Tinkerforge/master-brick/software/src/extensions/ethernet/ethernet_config.h

/* master-brick
 * Copyright (C) 2012-2014 Olaf Lüke <olaf@tinkerforge.com>
 *
 * ethernet_config.h: Configuration of Ethernet implementation
 *
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
 * You should have received a copy of the GNU Lesser General Public
 * License along with this library; if not, write to the
 * Free Software Foundation, Inc., 59 Temple Place - Suite 330,
 * Boston, MA 02111-1307, USA.
 */

#ifndef ETHERNET_CONFIG_H
#define ETHERNET_CONFIG_H

#include "bricklib/logging/logging.h"

#define ETHERNET_KEY (42 | (23 << 8) | (17 << 16) | (8 << 24))
#define ETHERNET_KEY_POS 4
#define ETHERNET_CONFIGURATION_POS 8
#define ETHERNET_HOSTNAME_POS (ETHERNET_CONFIGURATION_POS + sizeof(SetEthernetConfiguration) - sizeof(MessageHeader))
#define ETHERNET_WEBSOCKET_CONFIGURATION_POS (ETHERNET_HOSTNAME_POS + sizeof(SetEthernetHostname) - sizeof(MessageHeader))
#define ETHERNET_AUTHENTICATION_SECRET_KEY_POS (ETHERNET_WEBSOCKET_CONFIGURATION_POS + sizeof(SetEthernetWebsocketConfiguration) - sizeof(MessageHeader))
#define ETHERNET_AUTHENTICATION_SECRET_POS (4 + ETHERNET_AUTHENTICATION_SECRET_KEY_POS)
#define ETHERNET_MAC_POS (32*4)

#define ETHERNET_HOSTNAME_LENGTH 32

#define ETHERNET_CONNECTION_DHCP 0
#define ETHERNET_CONNECTION_STATIC 1

#define ETHERNET_MAX_DATA_LENGTH 80
#define ETHERNET_MAX_SOCKETS 7
#define ETHERNET_BUFFER_SIZE WIFI_MAX_DATA_LENGTH
#define ETHERNET_UDP_HEADER_SIZE 8

#define ETHERNET_USART_SPI_CLOCK 2000000

#define ETHERNET_W5200_READ_COMMAND    0x00
#define ETHERNET_W5200_WRITE_COMMAND   0x80
#define ETHERNET_W5500_READ_COMMAND    0x00
#define ETHERNET_W5500_WRITE_COMMAND   0x04

#define ETHERNET_CS_0        0
#define ETHERNET_CS_1        4
#define ETHERNET_RESET_0     1
#define ETHERNET_RESET_1     5
#define ETHERNET_INT_0       2
#define ETHERNET_INT_1       6
#define ETHERNET_PWDN_0      3
#define ETHERNET_PWDN_1      7

#define ETHERNET_MISO        8
#define ETHERNET_MOSI        9
#define ETHERNET_CLK        10

#define ETHERNET_RX_SIZE     2
#define ETHERNET_TX_SIZE     2
#define ETHERNET_MAC_SIZE    6
#define ETHERNET_IP_SIZE     4
#define ETHERNET_NUM_SOCKETS 8

#define ETHERNET_RX_BASE 0xC000
#define ETHERNET_TX_BASE 0x8000
#define ETHERNET_RX_MASK 0x07FF
#define ETHERNET_TX_MASK 0x07FF


#define DEBUG_ETHERNET 1

#if(DEBUG_ETHERNET)
#define logethd(str, ...) do{logd("eth: " str, ##__VA_ARGS__);}while(0)
#define logethi(str, ...) do{logi("eth: " str, ##__VA_ARGS__);}while(0)
#define logethw(str, ...) do{logw("eth: " str, ##__VA_ARGS__);}while(0)
#define logethe(str, ...) do{loge("eth: " str, ##__VA_ARGS__);}while(0)
#define logethf(str, ...) do{logf("eth: " str, ##__VA_ARGS__);}while(0)
#else
#define logethd(str, ...) {}
#define logethi(str, ...) {}
#define logethw(str, ...) {}
#define logethe(str, ...) {}
#define logethf(str, ...) {}
#endif

#endif
