Tinkerforge/master-brick/software/src/extensions/ethernet/ethernet_websocket.c

/* master-brick
 * Copyright (C) 2014 Olaf Lüke <olaf@tinkerforge.com>
 *
 * ethernet_websocket.c: Ethernet websocket implementation
 *
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
 * You should have received a copy of the GNU Lesser General Public
 * License along with this library; if not, write to the
 * Free Software Foundation, Inc., 59 Temple Place - Suite 330,
 * Boston, MA 02111-1307, USA.
 */

#include "ethernet_websocket.h"

#include <stdint.h>
#include <stdbool.h>
#include <string.h>

#include "config.h"
#include "ethernet_config.h"
#include "ethernet_low_level.h"
#include "extensions/websocket.h"
#include "extensions/brickd.h"

extern ComInfo com_info;

EthernetWebsocketState ethernet_websocket_state[ETHERNET_MAX_SOCKETS] = {
	WEBSOCKET_STATE_WAIT_FOR_HANDSHAKE,
	WEBSOCKET_STATE_WAIT_FOR_HANDSHAKE,
	WEBSOCKET_STATE_WAIT_FOR_HANDSHAKE,
	WEBSOCKET_STATE_WAIT_FOR_HANDSHAKE,
	WEBSOCKET_STATE_WAIT_FOR_HANDSHAKE,
	WEBSOCKET_STATE_WAIT_FOR_HANDSHAKE,
	WEBSOCKET_STATE_WAIT_FOR_HANDSHAKE
};

WebsocketFrame ethernet_websocket_frame[ETHERNET_MAX_SOCKETS] = {{0}};

uint8_t ethernet_websocket_to_read[ETHERNET_MAX_SOCKETS] = {0, 0, 0, 0, 0, 0, 0};
uint8_t ethernet_websocket_mask_mod[ETHERNET_MAX_SOCKETS] = {0, 0, 0, 0, 0, 0, 0};

#define ETHERNET_WEBSOCKET_ERROR_ANSWER_1 "HTTP/1.1 200 OK\r\nContent-Length: 276\r\nContent-Type: text/html\r\n\r\n"
#define ETHERNET_WEBSOCKET_ERROR_ANSWER_2 "<html><head><title>This is a Websocket</title></head><body>Dear Sir or Madam,<br/><br/>I regret to inform you that there is no webserver "
#define ETHERNET_WEBSOCKET_ERROR_ANSWER_3 "here.<br/>This port is exclusively used for Websockets.<br/><br/>Yours faithfully,<blockquote>Ethernet Extension</blockquote></body></html>"

void ethernet_websocket_init(const uint8_t socket) {
	ethernet_websocket_state[socket] = WEBSOCKET_STATE_WAIT_FOR_HANDSHAKE;
	ethernet_websocket_to_read[socket] = 0;
	ethernet_websocket_frame[socket].fin = 0;
	ethernet_websocket_frame[socket].mask = 0;
	ethernet_websocket_frame[socket].rsv1 = 0;
	ethernet_websocket_frame[socket].rsv2 = 0;
	ethernet_websocket_frame[socket].rsv3 = 0;
	ethernet_websocket_frame[socket].opcode = 0;
	ethernet_websocket_frame[socket].payload_length = 0;
	ethernet_websocket_frame[socket].masking_key[0] = 0;
	ethernet_websocket_frame[socket].masking_key[1] = 0;
	ethernet_websocket_frame[socket].masking_key[2] = 0;
	ethernet_websocket_frame[socket].masking_key[3] = 0;
}

void ethernet_websocket_answer_error(int32_t user_data) {
	if(user_data > 7) {
		return;
	}

	ethernet_low_level_write_data_tcp_blocking(user_data, (uint8_t*)ETHERNET_WEBSOCKET_ERROR_ANSWER_1, strlen(ETHERNET_WEBSOCKET_ERROR_ANSWER_1));
	ethernet_low_level_write_data_tcp_blocking(user_data, (uint8_t*)ETHERNET_WEBSOCKET_ERROR_ANSWER_2, strlen(ETHERNET_WEBSOCKET_ERROR_ANSWER_2));
	ethernet_low_level_write_data_tcp_blocking(user_data, (uint8_t*)ETHERNET_WEBSOCKET_ERROR_ANSWER_3, strlen(ETHERNET_WEBSOCKET_ERROR_ANSWER_3));
	ethernet_low_level_emergency_disconnect(user_data);
}

void ethernet_websocket_answer_callback(char *answer, uint8_t length, int32_t user_data) {
	if(user_data > 7) {
		return;
	}

	ethernet_low_level_write_data_tcp_blocking(user_data, (uint8_t*)WEBSOCKET_ANSWER_STRING_1, strlen(WEBSOCKET_ANSWER_STRING_1));
	ethernet_low_level_write_data_tcp_blocking(user_data, (uint8_t*)answer, length);
	ethernet_low_level_write_data_tcp_blocking(user_data, (uint8_t*)WEBSOCKET_ANSWER_STRING_2, strlen(WEBSOCKET_ANSWER_STRING_2));
	ethernet_websocket_state[user_data] = WEBSOCKET_STATE_HANDSHAKE_DONE;
	ethernet_websocket_to_read[user_data] = sizeof(WebsocketFrame);

	com_info.current = COM_ETHERNET;
}

uint8_t ethernet_websocket_write_data_tcp(const uint8_t socket, const uint8_t *buffer, const uint8_t length) {
	WebsocketFrameClientToServer wfcts;
	wfcts.fin = 1;
	wfcts.rsv1 = 0;
	wfcts.rsv2 = 0;
	wfcts.rsv3 = 0;
	wfcts.opcode = 2;
	wfcts.mask = 0;
	wfcts.payload_length = length;

	uint8_t length_to_send = sizeof(WebsocketFrameClientToServer) + length;
	uint8_t websocket_data[length_to_send];
	memcpy((void*)websocket_data, (void*)&wfcts, sizeof(WebsocketFrameClientToServer));
	memcpy((void*)(websocket_data + sizeof(WebsocketFrameClientToServer)), buffer, length);

	// For websockets we have to send the whole data package, otherwise
	// we may send the header more then once
	ethernet_low_level_write_data_tcp_blocking(socket, websocket_data, length_to_send);

	return length;
}

void ethernet_websocket_close_frame(const WebsocketFrame *wsf, const uint8_t socket) {
	uint8_t length = wsf->payload_length;
	uint8_t tmp_buffer[length];
	while(length > 0) {
		length -= ethernet_low_level_read_data_tcp(socket, tmp_buffer, length);
	}
	ethernet_low_level_disconnect(socket);
	brickd_disconnect(socket);

	ethernet_low_level_socket_init(socket);
	ethernet_low_level_socket_listen(socket);
	brickd_disconnect(socket);
}

uint8_t ethernet_websocket_read_data_tcp(const uint8_t socket, uint8_t *buffer, const uint8_t length) {
	uint8_t read_length = 0;
	switch(ethernet_websocket_state[socket]) {
		case WEBSOCKET_STATE_WAIT_FOR_HANDSHAKE: {
			uint8_t data[100];
			uint8_t handshake_length = ethernet_low_level_read_data_tcp(socket, data, 100);
			if(handshake_length != 0) {
				websocket_parse_handshake((char*)data, handshake_length, ethernet_websocket_answer_callback, ethernet_websocket_answer_error, socket);
			}

			return 0;
		}

		case WEBSOCKET_STATE_HANDSHAKE_DONE: {
			// buffer with max possible size of websocket header
			ethernet_websocket_frame[socket].fin = 1;
			ethernet_websocket_to_read[socket] -= ethernet_low_level_read_data_tcp(socket,
			                                                                       ((uint8_t*)&ethernet_websocket_frame[socket]) + (sizeof(WebsocketFrame) - ethernet_websocket_to_read[socket]),
			                                                                       ethernet_websocket_to_read[socket]);

			if(ethernet_websocket_to_read[socket] != 0) {
				return 0;
			}

			ethernet_websocket_state[socket] = WEBSOCKET_STATE_WEBSOCKET_HEADER_DONE;

			if(ethernet_websocket_frame[socket].mask != 1) {
				// mask = 0 from browser is not allowed!
				logethe("Mask=0 not allowed\n\r");
				ethernet_low_level_emergency_disconnect(socket);
				return 0;
			}

			// We currently don't support 16 bit or 64 bit length
			if(ethernet_websocket_frame[socket].payload_length == 126 || ethernet_websocket_frame[socket].payload_length == 127) {
				ethernet_low_level_emergency_disconnect(socket);
				return 0;
			}

			switch(ethernet_websocket_frame[socket].opcode) {
				case WEBSOCKET_OPCODE_CONTINUATION_FRAME:
				case WEBSOCKET_OPCODE_TEXT_FRAME: {
					// Continuation and text frame not allowed
					logethe("Opcode not supported: %d\n\r", ethernet_websocket_frame[socket].opcode);
					ethernet_low_level_emergency_disconnect(socket);
					return 0;
				}

				case WEBSOCKET_OPCODE_BINARY_FRAME: {
					ethernet_websocket_mask_mod[socket] = 0;
					ethernet_websocket_to_read[socket] = ethernet_websocket_frame[socket].payload_length;
					break;
				}

				case WEBSOCKET_OPCODE_CLOSE_FRAME: {
					ethernet_websocket_close_frame(&ethernet_websocket_frame[socket], socket);
					break;
				}

				case WEBSOCKET_OPCODE_PING_FRAME: {
					logethe("Opcode not supported: %d\n\r", ethernet_websocket_frame[socket].opcode);
					ethernet_low_level_emergency_disconnect(socket);
					break;
				}

				case WEBSCOKET_OPCODE_PONG_FRAME: {
					logethe("Opcode not supported: %d\n\r", ethernet_websocket_frame[socket].opcode);
					ethernet_low_level_emergency_disconnect(socket);
					break;
				}
			}

			return 0;
		}

		case WEBSOCKET_STATE_WEBSOCKET_HEADER_DONE: {
			// Websocket header is done, we can just read the data
			read_length = ethernet_low_level_read_data_tcp(socket, buffer, MIN(length, ethernet_websocket_to_read[socket]));

			for(uint8_t i = 0; i < read_length; i++) {
				buffer[i] ^= ethernet_websocket_frame[socket].masking_key[ethernet_websocket_mask_mod[socket]];
				ethernet_websocket_mask_mod[socket]++;
				if(ethernet_websocket_mask_mod[socket] >= WEBSOCKET_MASK_LENGTH) {
					ethernet_websocket_mask_mod[socket] = 0;
				}
			}

			ethernet_websocket_to_read[socket] -= read_length;
			if(ethernet_websocket_to_read[socket] == 0) {
				ethernet_websocket_state[socket] = WEBSOCKET_STATE_HANDSHAKE_DONE;
				ethernet_websocket_to_read[socket] = sizeof(WebsocketFrame);
			}

			break;
		}

		default: {
			logethe("Invalid Ethernet Websocket state: %d\n\r", (int)ethernet_websocket_state);
			break;
		}
	}

	return read_length;
}
