Tinkerforge/master-brick/software/src/extensions/ethernet/ethernet_low_level.h

/* master-brick
 * Copyright (C) 2012-2014 Olaf Lüke <olaf@tinkerforge.com>
 *
 * ethernet_low_level.h: Low level Ethernet protocol implementation
 *
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
 * You should have received a copy of the GNU Lesser General Public
 * License along with this library; if not, write to the
 * Free Software Foundation, Inc., 59 Temple Place - Suite 330,
 * Boston, MA 02111-1307, USA.
 */

#ifndef ETHERNET_LOW_LEVEL_H
#define ETHERNET_LOW_LEVEL_H

#include <stdint.h>

#include "ethernet_config.h"

typedef struct {
	uint32_t ETH_REG_MODE;
	uint32_t ETH_REG_GATEWAY_ADDRESS;
	uint32_t ETH_REG_SUBNET_MASK;
	uint32_t ETH_REG_SOURCE_HW_ADDRESS;
	uint32_t ETH_REG_SOURCE_IP_ADDRESS;
	uint32_t ETH_REG_RETRY_TIME;
	uint32_t ETH_REG_RETRY_COUNT;
	uint32_t ETH_REG_CHIP_VERSION;
	uint32_t CH_BASE;
	uint32_t CH_OFFSET_SHIFT;
} W5X00Register;

#define W5500_BSB_TX(s) ((2 + ((s) << 2)) << 3)
#define W5500_BSB_RX(s) ((3 + ((s) << 2)) << 3)

// Leave registers here for reference.
// We only put registers in the struct above if they are used, this saves space.
#if 0
#define ETH_REG_MODE                   0x0000
#define ETH_REG_GATEWAY_ADDRESS        0x0001
#define ETH_REG_SUBNET_MASK            0x0005
#define ETH_REG_SOURCE_HW_ADDRESS      0x0009
#define ETH_REG_SOURCE_IP_ADDRESS      0x000F
#define ETH_REG_INTERRUPT              0x0015
#define ETH_REG_INTERRUPT_MASK         0x0016
#define ETH_REG_RETRY_TIME             0x0017
#define ETH_REG_RETRY_COUNT            0x0019
#define ETH_REG_AUTH_TYPE              0x001C
#define ETH_REG_AUTH_ALGORITHM         0x001E
#define ETH_REG_CHIP_VERSION           0x001F
#define ETH_REG_PPP_LCP_REQUEST_TIMER  0x0028
#define ETH_REG_PPP_LCP_MAGIC_NUMBER   0x0029
#define ETH_REG_INTERRUPT_LOW_LEVEL    0x0030
#define ETH_REG_SOCKET_INTERRUPT       0x0034
#define ETH_REG_PHY_STATUS             0x0035
#define ETH_REG_SOCKET_INTERRUPT_MASK  0x0036
#endif

#define ETH_REG_OFFSET(s)               ((ethernet_regs->CH_BASE) + ((s) << (ethernet_regs->CH_OFFSET_SHIFT)))
#define ETH_REG_SN_MR(s)                (ETH_REG_OFFSET(s) + 0x000000)
#define ETH_REG_SN_CR(s)                (ETH_REG_OFFSET(s) + 0x000100)
#define ETH_REG_SN_IR(s)                (ETH_REG_OFFSET(s) + 0x000200)
#define ETH_REG_SN_SR(s)                (ETH_REG_OFFSET(s) + 0x000300)
#define ETH_REG_SN_PORT(s)              (ETH_REG_OFFSET(s) + 0x000400)
#define ETH_REG_SN_DHAR(s)              (ETH_REG_OFFSET(s) + 0x000600)
#define ETH_REG_SN_DIPR(s)              (ETH_REG_OFFSET(s) + 0x000C00)
#define ETH_REG_SN_DPORT(s)             (ETH_REG_OFFSET(s) + 0x001000)
#define ETH_REG_SN_MSSR(s)              (ETH_REG_OFFSET(s) + 0x001200)
#define ETH_REG_SN_PROTO(s)             (ETH_REG_OFFSET(s) + 0x001400)
#define ETH_REG_SN_TOS(s)               (ETH_REG_OFFSET(s) + 0x001500)
#define ETH_REG_SN_TTL(s)               (ETH_REG_OFFSET(s) + 0x001600)
#define ETH_REG_SN_RXMEM_SIZE(s)        (ETH_REG_OFFSET(s) + 0x001E00)
#define ETH_REG_SN_TXMEM_SIZE(s)        (ETH_REG_OFFSET(s) + 0x001F00)
#define ETH_REG_SN_TX_FSR(s)            (ETH_REG_OFFSET(s) + 0x002000)
#define ETH_REG_SN_TX_RD(s)             (ETH_REG_OFFSET(s) + 0x002200)
#define ETH_REG_SN_TX_WR(s)             (ETH_REG_OFFSET(s) + 0x002400)
#define ETH_REG_SN_RX_RSR(s)            (ETH_REG_OFFSET(s) + 0x002600)
#define ETH_REG_SN_RX_RD(s)             (ETH_REG_OFFSET(s) + 0x002800)
#define ETH_REG_SN_RX_WR(s)             (ETH_REG_OFFSET(s) + 0x002A00)
#define ETH_REG_SN_IMR(s)               (ETH_REG_OFFSET(s) + 0x002C00)
#define ETH_REG_SN_FRAG(s)              (ETH_REG_OFFSET(s) + 0x002D00)

#define ETH_VAL_MODE_SW_RESET          (1 << 7)
#define ETH_VAL_MODE_PB                (1 << 6)
#define ETH_VAL_MODE_PPOE              (1 << 3)

#define ETH_VAL_PHY_STATUS_LINK        (1 << 5)
#define ETH_VAL_PHY_STATUS_POWERDOWN   (1 << 3)

#define ETH_VAL_SN_MR_MULTI            (1 << 7)
#define ETH_VAL_SN_MR_MF               (1 << 6)
#define ETH_VAL_SN_MR_ND_MC            (1 << 5)
#define ETH_VAL_SN_MR_PROTO_CLOSED     (0 << 0)
#define ETH_VAL_SN_MR_PROTO_TCP        (1 << 0)
#define ETH_VAL_SN_MR_PROTO_UDP        (2 << 0)
#define ETH_VAL_SN_MR_PROTO_IPRAW      (3 << 0)
#define ETH_VAL_SN_MR_PROTO_MACRAW     (4 << 0)
#define ETH_VAL_SN_MR_PROTO_PPPOE      (5 << 0)


#define ETH_VAL_SN_CR_OPEN             0x01
#define ETH_VAL_SN_CR_LISTEN           0x02
#define ETH_VAL_SN_CR_CONNECT          0x04
#define ETH_VAL_SN_CR_DISCON           0x08
#define ETH_VAL_SN_CR_CLOSE            0x10
#define ETH_VAL_SN_CR_SEND             0x20
#define ETH_VAL_SN_CR_SEND_MAC         0x21
#define ETH_VAL_SN_CR_SEND_KEEP        0x22
#define ETH_VAL_SN_CR_RECV             0x40

#define ETH_VAL_SN_IR_PRECV            (1 << 7)
#define ETH_VAL_SN_IR_PFAIL            (1 << 6)
#define ETH_VAL_SN_IR_PNEXT            (1 << 5)
#define ETH_VAL_SN_IR_SEND_OK          (1 << 4)
#define ETH_VAL_SN_IR_TIMEOUT          (1 << 3)
#define ETH_VAL_SN_IR_RECV             (1 << 2)
#define ETH_VAL_SN_IR_DISCON           (1 << 1)
#define ETH_VAL_SN_IR_CON              (1 << 0)

#define ETH_VAL_SN_SR_SOCK_CLOSED      0x00
#define ETH_VAL_SN_SR_SOCK_INIT        0x13
#define ETH_VAL_SN_SR_SOCK_LISTEN      0x14
#define ETH_VAL_SN_SR_SOCK_ESTABLISHED 0x17
#define ETH_VAL_SN_SR_SOCK_CLOSE_WAIT  0x1C
#define ETH_VAL_SN_SR_SOCK_UDP         0x22
#define ETH_VAL_SN_SR_SOCK_IPRAW       0x32
#define ETH_VAL_SN_SR_SOCK_MACRAW      0x42
#define ETH_VAL_SN_SR_SOCK_PPOE        0x5F
#define ETH_VAL_SN_SR_SOCK_SYNSENT     0x15
#define ETH_VAL_SN_SR_SOCK_SYNRECV     0x16
#define ETH_VAL_SN_SR_SOCK_FIN_WAIT    0x18
#define ETH_VAL_SN_SR_SOCK_CLOSING     0x1A
#define ETH_VAL_SN_SR_SOCK_TIME_WAIT   0x1B
#define ETH_VAL_SN_SR_SOCK_LAST_ACK    0x1D
#define ETH_VAL_SN_SR_SOCK_ARP         0x01

#define ETH_VAL_SN_IMR_PRECV           (1 << 7)
#define ETH_VAL_SN_IMR_PFAIL           (1 << 6)
#define ETH_VAL_SN_IMR_PNEXT           (1 << 5)
#define ETH_VAL_SN_IMR_SENDOK          (1 << 4)
#define ETH_VAL_SN_IMR_TIMEOUT         (1 << 3)
#define ETH_VAL_SN_IMR_RECV            (1 << 2)
#define ETH_VAL_SN_IMR_DISCON          (1 << 1)
#define ETH_VAL_SN_IMR_CON             (1 << 0)

void ethernet_low_level_get_default_hostname(char hostname[ETHERNET_HOSTNAME_LENGTH]);
void ethernet_low_level_reset(void);
void ethernet_low_level_init(void);
void ethernet_low_level_check_config(void);
bool ethernet_low_level_discover_chip_version(void);
void ethernet_low_level_emergency_disconnect(const uint8_t socket);
void ethernet_low_level_disconnect(const uint8_t socket);
uint8_t ethernet_low_level_get_status(const uint8_t socket);
void ethernet_low_level_socket_init(const uint8_t socket);
void ethernet_low_level_socket_listen(const uint8_t socket);
uint16_t ethernet_low_level_get_received_data_length(const uint8_t socket);
uint16_t ethernet_low_level_get_free_data_length(const uint8_t socket);
uint16_t ethernet_low_level_get_transmit_pointer(const uint8_t socket);
void ethernet_low_level_set_transmit_pointer(const uint8_t socket, const uint16_t pointer);
uint8_t ethernet_low_level_write_data_tcp_blocking(const uint8_t socket, const uint8_t *buffer, const uint8_t length);
uint8_t ethernet_low_level_read_data_tcp(const uint8_t socket, uint8_t *buffer, const uint8_t length);
uint8_t ethernet_low_level_write_data_tcp(const uint8_t socket, const uint8_t *buffer, const uint8_t length);
uint16_t ethernet_low_level_read_data_udp(const uint8_t socket, uint8_t *buffer, const uint16_t length, uint8_t ip[4], uint16_t *port);
uint16_t ethernet_low_level_write_data_udp(const uint8_t socket, const uint8_t *buffer, const uint16_t length, const uint8_t ip[4], const uint16_t port);
uint16_t ethernet_low_level_get_receive_pointer(const uint8_t socket);
void ethernet_low_level_set_receive_pointer(const uint8_t socket, const uint16_t pointer);
void ethernet_low_level_set_retry_time(const uint16_t retry_time);
void ethernet_low_level_set_retry_count(const uint8_t retry_count);
void ethernet_select(void);
void ethernet_deselect(void);
uint8_t ethernet_transceive_byte(const uint8_t value);
uint8_t ethernet_read_register(const uint32_t address);
void ethernet_write_register(const uint32_t address, const uint8_t value);
extern uint8_t (*ethernet_read_buffer)(const uint32_t address, uint8_t *buffer, const uint16_t length);
extern uint8_t (*ethernet_write_buffer)(const uint32_t address, const uint8_t *buffer, const uint16_t length);

#endif
