Tinkerforge/master-brick/software/src/extensions/ethernet/ethernet_dhcp.h

/* master-brick
 * Copyright (C) 2012 Olaf Lüke <olaf@tinkerforge.com>
 *
 * ethernet_dhcp.h: DHCP implementation for Ethernet Extension
 *
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
 * You should have received a copy of the GNU Lesser General Public
 * License along with this library; if not, write to the
 * Free Software Foundation, Inc., 59 Temple Place - Suite 330,
 * Boston, MA 02111-1307, USA.
 */

#ifndef ETHERNET_DHCP_H
#define ETHERNET_DHCP_H

#include <stdint.h>
#include <stdbool.h>

#define DHCP_SOCKET             7

// DHCP state machine
#define	STATE_DHCP_DISCOVER	    1
#define	STATE_DHCP_REQUEST      2
#define	STATE_DHCP_LEASED       3
#define	STATE_DHCP_REREQUEST    4
#define	STATE_DHCP_RELEASE      5

#define	DHCP_MAX_RETRY          3
#define	DHCP_WAIT_TIME          5

#define DHCP_FLAGSBROADCAST     0x8000

// UDP port numbers for DHCP
#define	DHCP_SERVER_PORT        67 // from server to client
#define DHCP_CLIENT_PORT        68 // from client to server

// DHCP message OP code
#define DHCP_BOOTREQUEST        1
#define DHCP_BOOTREPLY          2

// DHCP message type
#define	DHCP_DISCOVER           1
#define DHCP_OFFER              2
#define	DHCP_REQUEST            3
#define	DHCP_DECLINE            4
#define	DHCP_ACK                5
#define DHCP_NAK                6
#define	DHCP_RELEASE            7
#define DHCP_INFORM             8

// DHCP retransmission timeout (ms)
#define DHCP_INITIAL_RTO        ( 4*1000000)
#define DHCP_MAX_RTO            (64*1000000)

#define DHCP_HTYPE10MB          1
#define DHCP_HTYPE100MB         2

#define DHCP_HLENETHERNET       6
#define DHCP_HOPS               0
#define DHCP_SECS               0

#define DHCP_MAGIC_COOKIE       0x63825363
#define DHCP_START_XID          0x12345678

#define DEFAULT_LEASETIME       0xFFFFFFFF // infinite lease time

// DHCP options and values (cf. RFC1533)
enum {
	padOption = 0,
	subnetMask = 1,
	timerOffset = 2,
	routersOnSubnet = 3,
	timeServer = 4,
	nameServer = 5,
	dns = 6,
	logServer = 7,
	cookieServer = 8,
	lprServer = 9,
	impressServer = 10,
	resourceLocationServer = 11,
	hostName = 12,
	bootFileSize = 13,
	meritDumpFile = 14,
	domainName = 15,
	swapServer = 16,
	rootPath = 17,
	extentionsPath = 18,
	IPforwarding = 19,
	nonLocalSourceRouting = 20,
	policyFilter = 21,
	maxDgramReasmSize = 22,
	defaultIPTTL = 23,
	pathMTUagingTimeout = 24,
	pathMTUplateauTable = 25,
	ifMTU = 26,
	allSubnetsLocal = 27,
	broadcastAddr = 28,
	performMaskDiscovery = 29,
	maskSupplier = 30,
	performRouterDiscovery = 31,
	routerSolicitationAddr = 32,
	staticRoute = 33,
	trailerEncapsulation = 34,
	arpCacheTimeout = 35,
	ethernetEncapsulation = 36,
	tcpDefaultTTL = 37,
	tcpKeepaliveInterval = 38,
	tcpKeepaliveGarbage = 39,
	nisDomainName = 40,
	nisServers = 41,
	ntpServers = 42,
	vendorSpecificInfo = 43,
	netBIOSnameServer = 44,
	netBIOSdgramDistServer = 45,
	netBIOSnodeType = 46,
	netBIOSscope = 47,
	xFontServer = 48,
	xDisplayManager = 49,
	dhcpRequestedIPaddr = 50,
	dhcpIPaddrLeaseTime = 51,
	dhcpOptionOverload = 52,
	dhcpMessageType = 53,
	dhcpServerIdentifier = 54,
	dhcpParamRequest = 55,
	dhcpMsg = 56,
	dhcpMaxMsgSize = 57,
	dhcpT1value = 58,
	dhcpT2value = 59,
	dhcpClassIdentifier = 60,
	dhcpClientIdentifier = 61,
	endOption = 255
};

typedef struct {
	uint8_t	op;
	uint8_t	htype;
	uint8_t	hlen;
	uint8_t	hops;
	uint32_t xid;
	uint16_t secs;
	uint16_t flags;
	uint8_t	ciaddr[4];
	uint8_t	yiaddr[4];
	uint8_t	siaddr[4];
	uint8_t	giaddr[4];
	uint8_t	chaddr[16];
	uint8_t	sname[64];
	uint8_t	file[128];
	uint8_t	OPT[312];
} __attribute__((__packed__)) DHCPMessage;

#define MAX_DHCP_OPT	16

typedef union LeaseTime {
	uint32_t l_val;
	uint8_t  c_val[4];
} LeaseTime;

void dhcp_tick(const uint8_t tick_type);
void dhcp_send_discover(const uint8_t s);
void dhcp_send_request(const uint8_t s);
void dhcp_send_release_decline(const uint8_t s, const char msgtype);
char dhcp_parse_msg(const uint8_t s, const uint32_t length);
bool dhcp_create_socket(const uint8_t s);
void dhcp_check_state(const uint8_t s);
void dhcp_check_timeout(void);
void dhcp_set_network(void);
char dhcp_check_leased_ip(void);
void dhcp_get_ip(void);
uint32_t dhcp_init_socket(const uint8_t s);

char int_to_char(const uint8_t value);


#endif
