Tinkerforge/master-brick/software/src/extensions/chibi/chibi_init.c

/* master-brick
 * Copyright (C) 2011 Olaf Lüke <olaf@tinkerforge.com>
 *
 * chibi_init.c: Chibi initialization
 *
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
 * You should have received a copy of the GNU Lesser General Public
 * License along with this library; if not, write to the
 * Free Software Foundation, Inc., 59 Temple Place - Suite 330,
 * Boston, MA 02111-1307, USA.
 */


#include "chibi_slave.h"
#include "chibi_master.h"
#include "chibi_config.h"
#include "extensions/extension_init.h"
#include "extensions/extension_i2c.h"
#include "bricklib/com/usb/usb.h"
#include "bricklib/utility/util_definitions.h"
#include "bricklib/logging/logging.h"

extern uint8_t chibi_address;
extern uint8_t chibi_slave_address[];
extern uint8_t chibi_master_address;
extern uint8_t chibi_frequency_mode;
extern uint8_t chibi_channel;

extern Pin extension_pins[];
extern ComInfo com_info;

uint8_t CHIBI_SELECT = CHIBI_SELECT_0;
uint8_t CHIBI_RESET = CHIBI_RESET_0;
uint8_t CHIBI_INT = CHIBI_INT_0;
uint8_t CHIBI_SLP_TR = CHIBI_SLP_TR_0;

void chibi_init_masterslave(const uint8_t extension) {
	if(extension == 0) {
		CHIBI_SELECT = CHIBI_SELECT_0;
		CHIBI_RESET = CHIBI_RESET_0;
		CHIBI_INT = CHIBI_INT_0;
		CHIBI_SLP_TR = CHIBI_SLP_TR_0;
	} else if(extension == 1) {
		CHIBI_SELECT = CHIBI_SELECT_1;
		CHIBI_RESET = CHIBI_RESET_1;
		CHIBI_INT = CHIBI_INT_1;
		CHIBI_SLP_TR = CHIBI_SLP_TR_1;
	}


	extension_pins[CHIBI_RESET].type = PIO_OUTPUT_0;
    extension_pins[CHIBI_SLP_TR].type = PIO_OUTPUT_1;
    PIO_Configure(&extension_pins[CHIBI_SELECT], 4);

    extension_pins[CHIBI_MISO].type = PIO_PERIPH_A;
    extension_pins[CHIBI_MOSI].type = PIO_PERIPH_A;
    extension_pins[CHIBI_CLK].type = PIO_PERIPH_B;
    PIO_Configure(&extension_pins[CHIBI_MISO], 3);

	extension_i2c_read(extension,
	                   CHIBI_ADDRESS_FREQUENCY,
	                   (char*)&chibi_frequency_mode,
	                   1);
	extension_i2c_read(extension,
	                   CHIBI_ADDRESS_CHANNEL,
	                   (char*)&chibi_channel,
	                   1);
	if(chibi_frequency_mode > 3) {
		chibi_frequency_mode = 0;
	}

	if(chibi_channel > 10) {
		chibi_channel = 0;
	}

	chibi_address = extension_get_address(extension);
	chibi_master_address = extension_get_master_address(extension);
	for(uint8_t i = 0; i < CHIBI_NUM_SLAVE_ADDRESS; i++) {
		chibi_slave_address[i] = extension_get_slave_address(extension, i);
		logi("chibi: For slave %d found address %d\n\r", i, chibi_slave_address[i]);
		if(chibi_slave_address[i] == 0) {
			break;
		}
	}

	chibi_init();

	if(chibi_address == chibi_master_address) {
		if(chibi_slave_address[0] == 0) {
			return;
		}
		com_info.ext_type[extension] = COM_TYPE_MASTER;
		chibi_master_init();
	} else {
		com_info.ext_type[extension] = COM_TYPE_SLAVE;
		chibi_slave_init();
	}

}
